yuhkm/STM32_Calculator_Keypad/Keypad_F401RET6_REV_4.5/Core/Inc/calError.h

//=============================================================================
//  calError.h
//
//  Programed by Yuhwan Kim
//=============================================================================

#ifndef CAL_ERROR_H
#define CAL_ERROR_H



//Postfix
extern int calError_Run(int errCode);




#endif
