yuhkm/STM32_Calculator_Keypad/Keypad_F401RET6_REV_4.5/Core/Inc/calOper.h

//=============================================================================
//  calOper.h
//
//  Programed by Yuhwan Kim
//=============================================================================

#ifndef CAL_CALCULATE_H
#define CAL_CALCULATE_H



//Calculate
extern int calOper_Run(char caInput[], TCalBuf* tpBuf);




#endif
