yuhkm/STM32_Calculator_Keypad/Keypad_F401RET6_REV_4.5/Core/Inc/calPostfix.h

//=============================================================================
//  calPostfix.h
//
//  Programed by Yuhwan Kim
//=============================================================================

//#ifndef INC_CALPOSTFIX_H_
//#define INC_CALPOSTFIX_H_

#ifndef CAL_POSTFIX_H
#define CAL_POSTFIX_H



//Postfix
extern int calPostfix_Run(char* cpInput, TCalBuf* tpBuf);




#endif
