yuhkm/STM32_Calculator_Keypad/Keypad_F401RET6_REV_4.5/Core/Inc/calStd.h

//=============================================================================
//  calStd.h
//
//  Programed by Yuhwan Kim
//=============================================================================

#ifndef CAL_STD_H
#define CAL_STD_H

#include <stdio.h>
#include <stdlib.h>
#include <string.h>
#include <ctype.h>
#include <math.h>





#endif
