yuhkm/STM32_Calculator_Keypad/Keypad_F401RET6_REV_4.5/Core/Inc/calculator.h

//=============================================================================
//  calculator.h
//
//  Programed by Yuhwan Kim
//=============================================================================

#ifndef CALCULATE_H
#define CALCULATE_H

void calculator_run(char caInput[]);



#endif
