yuhkm/STM32_Calculator_Keypad/Keypad_F401RET6_REV_4.5/Core/Inc/hidKeypad.h

//=============================================================================
//  hidKeypad.h
//
//  Programed by Yuhwan Kim
//=============================================================================


#ifndef INC_HIDKEYPAD_H_
#define INC_HIDKEYPAD_H_


#include "stm32f4xx_hal.h"
#include "usbd_hid.h"



void hidKeypad_sandKey(uint8_t key);
void hidKeypad_mecroTest();



#endif /* INC_HIDKEYPAD_H_ */
