yuhkm/STM32_Calculator_Keypad/Keypad_F401RET6_REV_4.5/Core/Inc/keypadMode.h

//=============================================================================
//  keypadMode.h
//
//  Programed by Yuhwan Kim
//=============================================================================


#ifndef INC_KEYPADMODE_H_
#define INC_KEYPADMODE_H_


#include "stm32f4xx_hal.h"



int keypadMode_read(void);



#endif /* INC_KEYPADMODE_H_ */
