yuhkm/STM32_Calculator_Keypad/Keypad_F401RET6_REV_4.5/Core/Inc/readBattery.h

/*
 * readBattery.h
 *
 *  Created on: Oct 6, 2024
 *      Author: yuhkm
 */

#ifndef INC_READBATTERY_H_
#define INC_READBATTERY_H_


char* readBattery_run();
void printBattery();


#endif /* INC_READBATTERY_H_ */
