yuhkm/STM32_Calculator_Keypad/Keypad_F401RET6_REV_4.5/Core/Inc/readKeypad.h

//=============================================================================
//  readKeypad.h
//
//  Programed by Yuhwan Kim
//=============================================================================


#ifndef INC_READKEYPAD_H_
#define INC_READKEYPAD_H_


#include "stm32f4xx_hal.h"



char readKeypad_run(void);



#endif /* INC_READKEYPAD_H_ */
