yuhkm/STM32_Calculator_Keypad/Keypad_F401RET6_REV_4.5/Core/Src/calculator.c

//=============================================================================
//  calculator.c
//
//  Programed by Yuhwan Kim
//=============================================================================

#include "calDef.h"
#include "calStd.h"
#include "calError.h"
#include "calStack.h"
#include "calPostfix.h"
#include "calOper.h"


void calculator_run(char caInput[])
{

	int nSt;

	TCalBuf tCalBuf;
	memset(&tCalBuf, 0, sizeof(tCalBuf));


	nSt = calPostfix_Run(caInput, &tCalBuf);
	nSt = calOper_Run(caInput, &tCalBuf);
}
